gsyi5839-alt/Ultra-TM02-/UI_Screenshots/超低温温度测量模块_使用说明书.md

# 超低温温度测量模块 使用说明书

## 文档信息

| 项目 | 内容 |
|---|---|
| 产品型号 | Ultra-TM02 |
| 产品名称 | 超低温温度测量模块 |
| 文档类型 | 使用说明书 |
| 适用对象 | 技术人员、操作人员 |

---

## 目录

- 第一章 面板介绍
- 第二章 上位机软件使用说明
- 第三章 装置主要参数
- 第四章 服务与支持

---

# 超低温温度测量模块简介

## 产品概述

Ultra-TM02型超低温温度测量模块是用于**二极管式温度探头**进行超低温测量的变换模块，用于将二极管的节电压转换为对应的温度并进行输出和显示。本模块适用于二极管式温度探头，且允许用户自己更新探头的分度表，适用于多种环境下的低温测量。

## 系统结构

### 系统框图

```
┌─────────────────────────────────────────────────────────────────────────┐
│                                                                         │
│    ┌─────────┐                    ┌─────────┐                          │
│    │ LCD电路  │◄────USART────────│         │         RS485            │
│    └─────────┘                    │         │◄────────────────►外部设备│
│                                   │         │         USB              │
│                                   │ 主控电路 │◄────────────────►PC     │
│    ┌─────────┐     ┌─────────┐   │         │                          │
│    │ 隔离    │     │ 隔离    │   │         │                          │
│    │ 电路1   │◄────│ 电路    │◄──│         │                          │
│    └────┬────┘     └─────────┘   └─────────┘                          │
│         │              │              ↑                                │
│         │    SPI       │              │                                │
│    ┌────┴────┐         │         ┌────┴────┐                          │
│    │ 隔离电路1│         │         │ 隔离电路2│                          │
│    └────┬────┘         │         └────┬────┘                          │
│         │              │              │                                │
│         ↓              │              ↓                                │
│  ┌──────────────────────────────────────────────────────────────┐     │
│  │                                                              │     │
│  │  ┌────────┐  ┌────────┐  ┌────────┐  ┌────────┐  ┌────────┐│     │
│  │  │电源电路│  │ 0.05%  │  │ DA电路 │  │ V/I电路│  │输出电路││→探头接口│
│  │  │ +9V    │  │ 电压   │  ├────────┤  ├────────┤  ├────────┤│     │
│  │  │ +5V    │  │ 参考   │  │ AD电路 │  │输入电路│  │        ││     │
│  │  │ +3.3V  │  │ 电路   │  └────────┘  └────────┘  └────────┘│     │
│  │  └────────┘  └────────┘                                    │     │
│  │                        ┌────────┐                          │     │
│  │                        │保护电路│                          │     │
│  │                        └────────┘                          │     │
│  └──────────────────────────────────────────────────────────────┘     │
│                                                                         │
└─────────────────────────────────────────────────────────────────────────┘
```

### 电路模块说明

| 模块 | 功能描述 |
|---|---|
| **电源电路** | 将AC 220V转换成+9V、+5V以及+3.3V供模块中的各个电路使用 |
| **主控电路** | 用于控制其它电路协同运行，实现模块的基本功能 |
| **LCD电路** | 主控电路通过USART与LCD电路进行通讯，以显示模块工作状态 |
| **RS485电路** | 主控电路使用USART配合RS485电路实现模块的通讯功能 |
| **USB电路** | 主控电路使用USART配合USB电路实现模块的通讯功能 |
| **隔离电路1** | 主控电路使用SPI经隔离电路1与D/A电路和A/D电路通讯，并控制它们进行输出和输入 |
| **隔离电路2** | 主控电路使用IO经隔离电路2控制(4-20)mA电流源进行电流输出 |
| **D/A电路** | 数模转换，输出电压信号 |
| **A/D电路** | 模数转换，采集输入信号 |
| **V/I电路** | 电压到电流转换 |
| **0.05%电压参考电路** | 提供高精度参考电压，保障模块的指标 |
| **保护电路** | 保护D/A电路、A/D电路、V/I电路、输出电路、输入电路以及0.05%电压参考电路 |

### 信号流程

1. **D/A电路**在主控电路的控制下输出电压信号
2. 该信号经过**V/I电路**变换为电流信号
3. 电流信号经过**输出电路**输出到探头
4. **输入电路**将探头中二极管的节点压信号引入
5. 经**A/D电路**变换为数字量
6. 进行换算与显示

---

# 第一章 面板介绍

## 1.1 主机前面板

### 前面板外观

```
┌─────────────────────────────────────────────────────────────┐
│                                                       ①    │
│              超 低 温 温 度 测 试 模 块                      │
│                                                             │
│                 T = -XXX.XXX  ℃                            │
│                                                             │
│              Vpn：XXXX.XXX mV                               │
│                                                             │
│  ②                                                         │
└─────────────────────────────────────────────────────────────┘
                    超低温温度测量模块 前面板
```

### 前面板显示说明

| 标号 | 显示内容 | 说明 |
|---|---|---|
| ① | T = -XXX.XXX ℃ | 测量结果显示区域，显示分辨力为**0.001℃** |
| ② | Vpn: XXXX.XXX mV | 二极管节电压显示，单位为**mV** |

## 1.2 主机前面板按键/端口功能介绍

| 序号 | 功能 | 详细说明 |
|---|---|---|
| 1 | 测量结果显示区域 | 显示分辨力为0.001℃，显示范围覆盖1.4K~500K |
| 2 | 二极管节电压显示 | 显示单位为mV，用于显示探头二极管的节点电压 |

---

## 1.3 主机背板1

### 背板1外观

```
┌─────────────────────────────────────────────────────────────┐
│     ●                      ●                         ①     │
│  ┌──────────────────┐                              ┌────┐  │
│  │                  │                              │▓▓▓▓│  │
│  │     4-20mA       │                              │▓▓▓▓│  │
│  │                  │                              └────┘  │
│  └──────────────────┘                                ②     │
│     ●                      ●                               │
└─────────────────────────────────────────────────────────────┘
                    超低温温度测量模块背板1
```

## 1.4 主机背板1端口介绍

| 序号 | 接口类型 | 功能说明 |
|---|---|---|
| **①** | **(4-20)mA输出接口** | 两线制电流输出接口 |
| **②** | **TypeC接口** | 与上位机软件配套使用，实现模块参数设定 |

### (4-20)mA输出接口使用注意

> ⚠️ **注意：使用时注意+端标记。**

本接口为**(4-20)mA两线制**接法，外部通讯设备如果不具备供电电源，需提供**24V电源**，接法如下图：

```
┌────────────────────────────────────────────────────────────────┐
│                                                                │
│   ┌──────────────────────┐      +        ┌──────────────────┐ │
│   │                      │───────────────│  显示/采集设备   │ │
│   │  超低温温度测量模块   │               │  内部不具备24V供电│ │
│   │                      │───────────────│                  │ │
│   └──────────────────────┘               └────────┬─────────┘ │
│                                                    │           │
│                                              24V供电           │
│                                                                │
└────────────────────────────────────────────────────────────────┘
```

### TypeC接口说明

TypeC接口用于与上位机软件配套使用，可以实现模块参数的设定，包括：
- 电流源选择与调整
- (4-20)mA输出范围设定
- 分度表加载
- 设备参数存储

---

## 1.5 主机背板2

### 背板2外观

```
┌─────────────────────────────────────────────────────────────┐
│     ●                     ⊕                          ●     │
│                                                             │
│                         探头                                │
│                                                             │
│     ●                     ⊕                          ●     │
└─────────────────────────────────────────────────────────────┘
                    超低温温度测量模块背板2
```

### 探头接口说明

主机背板2为**探头接口**，用户根据需求在该接口安装探头即可。

| 接口特性 | 说明 |
|---|---|
| 接口类型 | 4引线差分方式 |
| 适用探头 | 二极管式温度探头 |
| 连接方式 | 插接式 |

---

# 第二章 上位机软件使用说明

## 2.1 串行口的选择

如果用户需要对模块的基础设定进行更改，需要使用本模块配套的**上位机软件**。

> ⚠️ **注意：使用上位机软件对模块参数进行修改需由专业技术人员进行，参数的修改可能会造成设备参数产生偏离。**

### 软件安装步骤

在使用上位机软件之前，需要按照以下步骤进行软件的安装：

| 步骤 | 安装内容 | 说明 |
|---|---|---|
| **A** | VCP_V1.4.0_Setup | 安装【stm32驱动安装】文件夹中的VCP_V1.4.0_Setup软件 |
| **B** | USB驱动 | 安装U盘中【USB驱动】文件夹中的对应软件 |
| **C** | NI4882_1850f1 | 安装NI4882_1850f1 |

### USB驱动选择说明

| 系统类型 | 驱动文件 |
|---|---|
| 32位 Windows系统 | dpinst_x86 |
| 64位 Windows系统 | dpinst_amd64 或 dpinst_ia64 |

> 根据电脑的硬件情况安装1个即可。

### 启动软件

完成以上安装后，使用**typeC线**将模块与电脑连接，启动**TempDownloader软件**，可以看到以下界面：

---

## 2.2 上位机软件界面

### 软件主界面

```
┌──────────────────────────────────────────────────────────────┐
│  超低温温度计                                           [X]  │
├──────────────────────────────────────────────────────────────┤
│                                                              │
│  串行口：[ASRL13::INSTR     ▼]                              │
│                                                              │
│  设备ID：[                    ]     [获取设备ID]             │
│                                                              │
├────────────────────────┬─────────────────────────────────────┤
│       电流源            │           (4-20)mA                  │
├────────────────────────┼─────────────────────────────────────┤
│  ◉ 10uA    ○ 17uA     │  4mA代表温度点：[        ] ℃       │
│                        │                                     │
│  10uA调整值：[    ] uA │  20mA代表温度点：[        ] ℃      │
│  17uA调整值：[    ] uA │                                     │
│                        │                                     │
│  [  电流源调整  ]      │        [(4-20)mA调整]              │
├────────────────────────┴─────────────────────────────────────┤
│                                                              │
│  [开始采集]  [停止采集]  [加载分度表]  [存储参数]           │
│                                                              │
└──────────────────────────────────────────────────────────────┘
                       上位机软件界面示意图
```

### 界面功能区域说明

| 区域 | 功能 | 说明 |
|---|---|---|
| **串行口** | 下拉选择串口 | 选择与模块对应的串行口 |
| **设备ID** | 设备识别 | 输入或获取设备ID |
| **电流源** | 电流源选择 | 可选择10μA或17μA |
| **电流源调整** | 微调电流值 | 对电流源进行精细调整 |
| **(4-20)mA** | 输出范围设定 | 设置4mA和20mA对应的温度点 |

---

## 2.3 连接与通讯

### 操作步骤

1. 在串行口对应的下拉框中选择与模块对应的串行口
2. 点击**【停止采集】**按钮
3. 点击**【获取设备ID】**按钮确认通讯成功

---

## 2.4 电流源的选择与微调

### 电流源选择

用户可选择**10μA**或**17μA**作为模块输出电流。

| 电流源 | 适用场景 |
|---|---|
| 10μA | 标准二极管探头 |
| 17μA | 特定型号二极管探头 |

### 电流源微调

若校准后发现电流存在偏差，可进行微调：

1. 选择对应的电流源（10μA或17μA）
2. 在调整值输入框中输入调整量
3. 配合数字多用表测量实际输出
4. 调整至结果达标后点击**【电流源调整】**
5. 点击**【存储参数】**按钮保存设置至模块Flash

---

## 2.5 4mA~20mA输出调整

### 功能说明

本模块支持**4mA至20mA节点调整**功能：

| 设置项 | 说明 |
|---|---|
| 4mA代表温度点 | 用户可自定义4mA电流对应的最低温度点 |
| 20mA代表温度点 | 用户可自定义20mA电流对应的最高温度点 |

> 无需使用模块出厂默认的调整方式

### 操作方法

1. 在对应输入框中输入温度点数值
2. 点击**【(4-20)mA调整】**按钮
3. 点击**【存储参数】**按钮完成设置

---

## 2.6 开始采集与停止采集按钮

这两个按钮用于控制模块进行**数据采集**操作：

| 按钮 | 功能 |
|---|---|
| **开始采集** | 启动模块的数据采集过程 |
| **停止采集** | 终止模块的数据采集过程 |

> ⚠️ **注意：在用本软件下载参数前，应点击【停止采集】按钮来停止模块进行数据采集。**

---

## 2.7 【加载分度表】按钮

### 功能说明

用户可以通过**【加载分度表】**按钮：
- 为新探头加载新的分度表
- 对特定探头的分度表进行修改和优化

### 分度表格式要求

> ⚠️ **注意：待加载的分度表应符合软件的具体要求。**

分度表文件格式需符合软件规定的具体要求，详见软件帮助文档。

---

## 2.8 【存储参数】按钮

点击**【存储参数】**按钮可将当前设置保存至模块内部Flash存储器。

模块重启后将按用户所设参数运行。

---

# 第三章 装置主要参数

## 主要参数一览表

| 序号 | 参数项 | 规格 |
|---|---|---|
| 1 | **温度测量范围** | 1.4K ~ 500K |
| 2 | **测量结果显示单位** | ℃ |
| 3 | **显示分辨率** | 0.001℃ |
| 4 | **最大允许误差（低温段）** | ±1℃ |
| 5 | **最大允许误差（高温段）** | ±2℃ |
| 6 | **A/D位数** | 24位 |
| 7 | **内部电流源最大运行误差** | 优于0.05% |
| 8 | **数据更新率** | 最高1次/s |
| 9 | **内部Flash曲线支持** | 1条4871点曲线下载 |
| 10 | **供电电压** | 220Vac |
| 11 | **探头类型** | 二极管探头（4引线差分方式） |
| 12 | **显示屏** | 3.5寸液晶显示 |
| 13 | **输出形式** | (4-20)mA |

---

## 特色功能

| 功能 | 说明 |
|---|---|
| **A. 可重新下载探头参数表** | 支持用户自定义探头分度表，适应不同探头特性 |
| **B. 具备USB接口** | 可与PC直连，方便参数设置和数据传输 |
| **C. 兼容多种导通电流探头** | 兼容10μA、17μA等不同导通电流的二极管温探头，可根据需求设置导通电流 |

---

## 技术规格详细说明

### 温度测量

| 参数 | 数值 | 说明 |
|---|---|---|
| 测量范围 | 1.4K ~ 500K | -271.75℃ ~ +226.85℃ |
| 分辨率 | 0.001℃ | 1mK |
| 低温段精度 | ±1℃ | 适用于低温区域 |
| 高温段精度 | ±2℃ | 适用于高温区域 |

### 电气特性

| 参数 | 数值 |
|---|---|
| 供电电压 | AC 220V |
| A/D转换精度 | 24位 |
| 电流源精度 | ≤0.05% |
| 电流源选择 | 10μA / 17μA |

### 输出特性

| 参数 | 数值 |
|---|---|
| 输出类型 | 4-20mA电流环 |
| 接线方式 | 两线制 |
| 外部供电 | 24V（当外部设备不具备供电时） |

### 存储特性

| 参数 | 数值 |
|---|---|
| 分度表存储 | 内部Flash |
| 最大点数 | 4871点/条曲线 |
| 曲线条数 | 1条 |

### 显示特性

| 参数 | 数值 |
|---|---|
| 显示屏尺寸 | 3.5寸 |
| 显示类型 | 液晶显示 |
| 温度显示 | T = XXX.XXX ℃ |
| 电压显示 | Vpn: XXXX.XXX mV |

---

# 第四章 服务与支持

## 技术支持

如有任何技术问题，请联系产品供应商获取技术支持。

## 保修说明

请参阅产品保修卡了解详细保修条款。

---

# 附录

## 附录A：模块及附件清单

| 序号 | 名称 | 数量 | 备注 |
|---|---|---|---|
| 1 | 超低温温度测量模块主机 | 1台 | - |
| 2 | 电源线（交流版） | 1条 | AC 220V |
| 3 | U盘 | 1块 | 内含校正软件、说明书 |
| 4 | 4线PTFE转接线 | 1条 | 探头连接用 |
| 5 | Lemo连接器接头（备用） | 1个 | 备件 |
| 6 | 使用说明书 | 1本 | 本文档 |

## 附录B：软件安装文件清单

| 文件夹/文件 | 说明 |
|---|---|
| stm32驱动安装/VCP_V1.4.0_Setup | STM32虚拟串口驱动 |
| USB驱动/dpinst_x86 | 32位Windows USB驱动 |
| USB驱动/dpinst_amd64 | 64位Windows USB驱动(AMD64) |
| USB驱动/dpinst_ia64 | 64位Windows USB驱动(IA64) |
| NI4882_1850f1 | NI-VISA驱动 |
| TempDownloader | 上位机软件 |

## 附录C：常见问题解答

### Q1: 如何选择正确的串行口？

A: 连接模块后，在设备管理器中查看新增的COM端口号，然后在软件中选择对应的串行口。

### Q2: 为什么获取不到设备ID？

A: 请检查：
1. USB线缆连接是否正常
2. 驱动是否正确安装
3. 串行口选择是否正确
4. 是否点击了【停止采集】按钮

### Q3: 如何校准电流源？

A: 
1. 选择对应的电流源（10μA或17μA）
2. 使用高精度数字多用表测量实际输出电流
3. 在调整值中输入偏差量
4. 点击【电流源调整】后再次测量
5. 调整满意后点击【存储参数】保存

---

*本文档基于产品说明书截图整理*
*版本：V1.0*
