gsyi5839-alt/Ultra-TM02-/Schematics/01.png

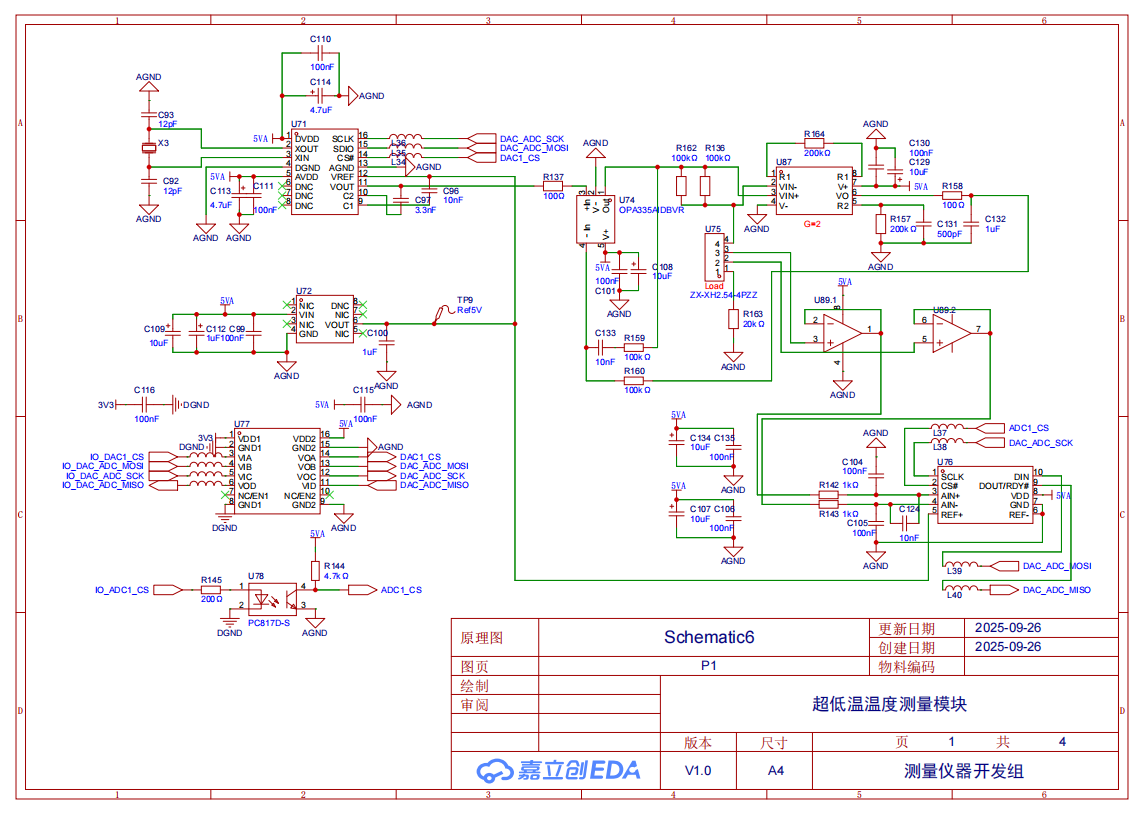
Schematics/01.png
