gsyi5839-alt/Ultra-TM02-/Schematics/02.png

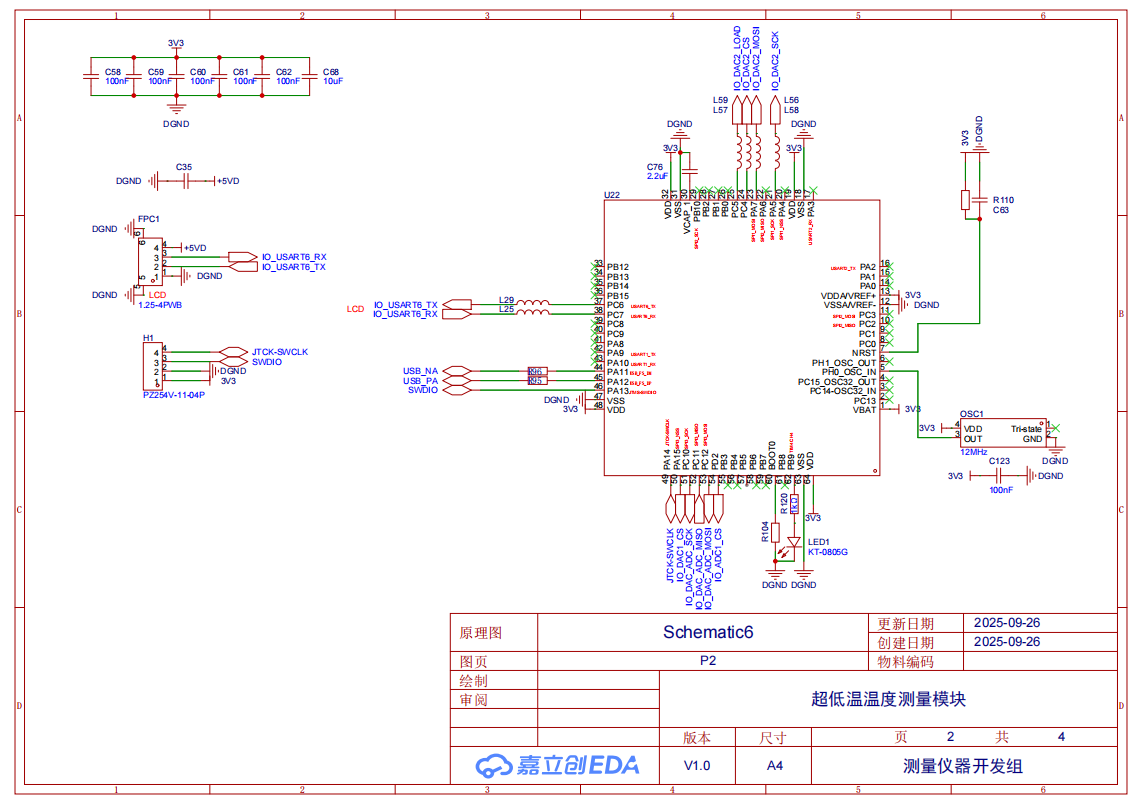
Schematics/02.png
