gsyi5839-alt/Ultra-TM02-/Schematics/03.png

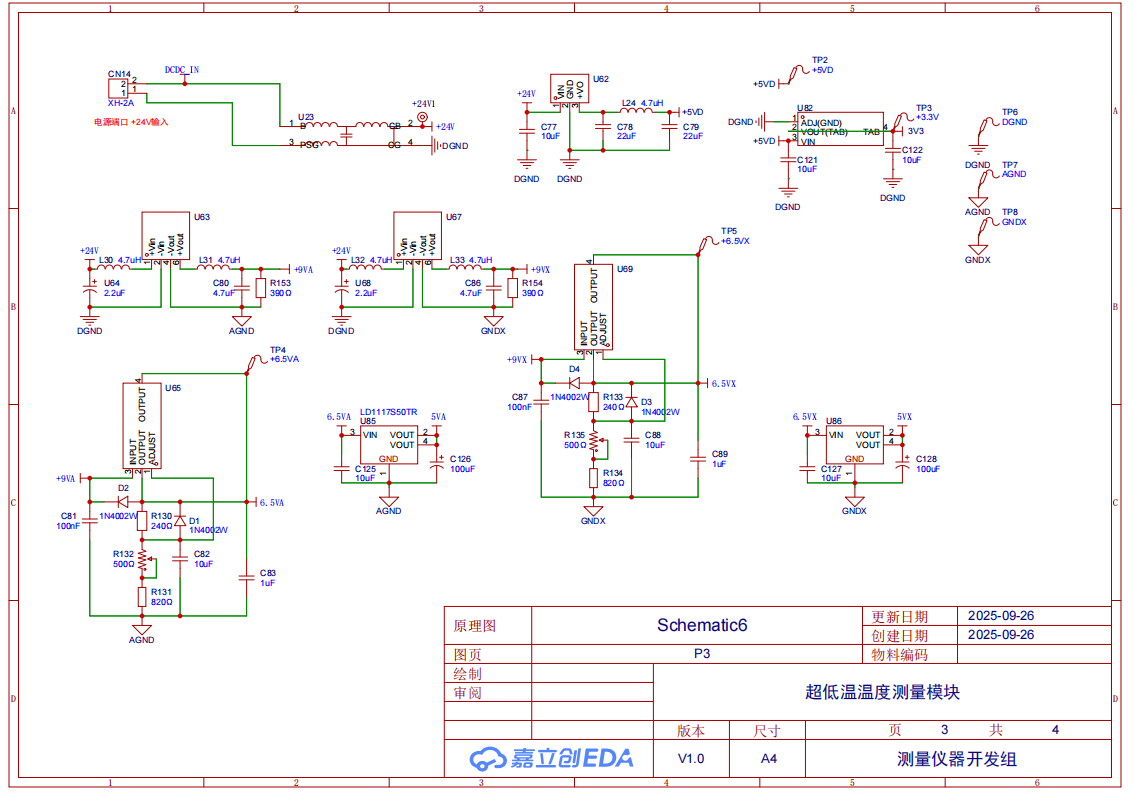
Schematics/03.png
