gsyi5839-alt/Ultra-TM02-/Schematics/04.png

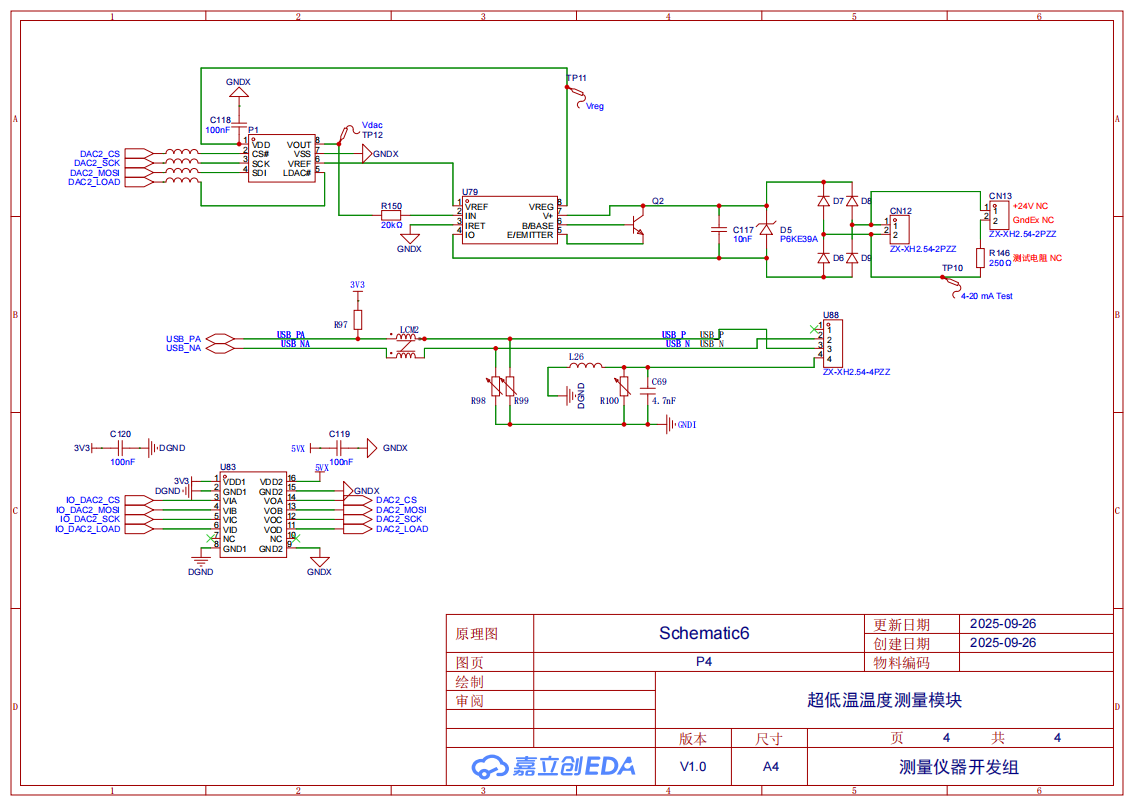
Schematics/04.png
