gsyi5839-alt/Ultra-TM02-/UI_Screenshots/07_Chapter3_Main_Parameters.png

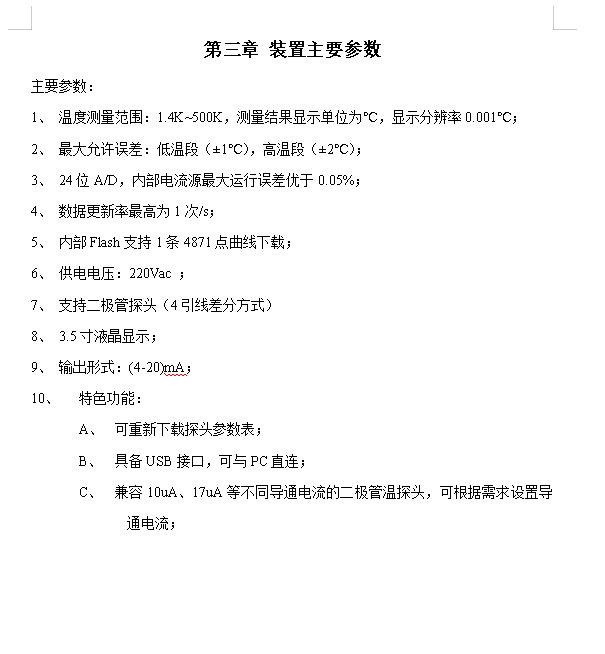
UI_Screenshots/07_Chapter3_Main_Parameters.png
